Dovgalyuk/MRRSoundDecoder/esp32/components/sd/sd.c

/* SD card and FAT filesystem example.
   This example uses SPI peripheral to communicate with SD card.

   This example code is in the Public Domain (or CC0 licensed, at your option.)

   Unless required by applicable law or agreed to in writing, this
   software is distributed on an "AS IS" BASIS, WITHOUT WARRANTIES OR
   CONDITIONS OF ANY KIND, either express or implied.
*/

#include <string.h>
#include <sys/unistd.h>
#include <sys/stat.h>
#include "esp_vfs_fat.h"
#include "sdmmc_cmd.h"
//#include "sd_test_io.h"
#if SOC_SDMMC_IO_POWER_EXTERNAL
#include "sd_pwr_ctrl_by_on_chip_ldo.h"
#endif

static const char *TAG = "sd";

// Pin assignments can be set in menuconfig, see "SD SPI Example Configuration" menu.
// You can also change the pin assignments here by changing the following 4 lines.
#define PIN_NUM_MISO  CONFIG_SD_PIN_MISO
#define PIN_NUM_MOSI  CONFIG_SD_PIN_MOSI
#define PIN_NUM_CLK   CONFIG_SD_PIN_CLK
#define PIN_NUM_CS    CONFIG_SD_PIN_CS

void sd_init(const char *mount_point)
{
    esp_err_t ret;

    // Options for mounting the filesystem.
    esp_vfs_fat_sdmmc_mount_config_t mount_config = {
        .format_if_mount_failed = false,
        .max_files = 3,
        .allocation_unit_size = 8 * 1024
    };
    sdmmc_card_t *card;
    ESP_LOGI(TAG, "Initializing SD card");

    // Use settings defined above to initialize SD card and mount FAT filesystem.
    // Note: esp_vfs_fat_sdmmc/sdspi_mount is all-in-one convenience functions.
    // Please check its source code and implement error recovery when developing
    // production applications.
    ESP_LOGI(TAG, "Using SPI peripheral");

    // By default, SD card frequency is initialized to SDMMC_FREQ_DEFAULT (20MHz)
    // For setting a specific frequency, use host.max_freq_khz (range 400kHz - 20MHz for SDSPI)
    // Example: for fixed frequency of 10MHz, use host.max_freq_khz = 10000;
    sdmmc_host_t host = SDSPI_HOST_DEFAULT();

    // For SoCs where the SD power can be supplied both via an internal or external (e.g. on-board LDO) power supply.
    // When using specific IO pins (which can be used for ultra high-speed SDMMC) to connect to the SD card
    // and the internal LDO power supply, we need to initialize the power supply first.
#if CONFIG_EXAMPLE_SD_PWR_CTRL_LDO_INTERNAL_IO
    sd_pwr_ctrl_ldo_config_t ldo_config = {
        .ldo_chan_id = CONFIG_EXAMPLE_SD_PWR_CTRL_LDO_IO_ID,
    };
    sd_pwr_ctrl_handle_t pwr_ctrl_handle = NULL;

    ret = sd_pwr_ctrl_new_on_chip_ldo(&ldo_config, &pwr_ctrl_handle);
    if (ret != ESP_OK) {
        ESP_LOGE(TAG, "Failed to create a new on-chip LDO power control driver");
        return;
    }
    host.pwr_ctrl_handle = pwr_ctrl_handle;
#endif

    spi_bus_config_t bus_cfg = {
        .mosi_io_num = PIN_NUM_MOSI,
        .miso_io_num = PIN_NUM_MISO,
        .sclk_io_num = PIN_NUM_CLK,
        .quadwp_io_num = -1,
        .quadhd_io_num = -1,
        .max_transfer_sz = 4000,
    };

    /* Enable pullup for faster operation */
    gpio_set_direction(PIN_NUM_CLK, GPIO_MODE_INPUT_OUTPUT_OD);
    gpio_set_direction(PIN_NUM_CS, GPIO_MODE_INPUT_OUTPUT_OD);
    gpio_set_direction(PIN_NUM_MOSI, GPIO_MODE_INPUT_OUTPUT_OD);
    gpio_set_direction(PIN_NUM_MISO, GPIO_MODE_INPUT_OUTPUT_OD);
    gpio_pullup_en(PIN_NUM_CLK);
    gpio_pullup_en(PIN_NUM_CS);
    gpio_pullup_en(PIN_NUM_MOSI);
    gpio_pullup_en(PIN_NUM_MISO);

    ret = spi_bus_initialize(host.slot, &bus_cfg, SDSPI_DEFAULT_DMA);
    if (ret != ESP_OK) {
        ESP_LOGE(TAG, "Failed to initialize bus.");
        return;
    }

    // This initializes the slot without card detect (CD) and write protect (WP) signals.
    // Modify slot_config.gpio_cd and slot_config.gpio_wp if your board has these signals.
    sdspi_device_config_t slot_config = SDSPI_DEVICE_CONFIG_DEFAULT();
    slot_config.gpio_cs = PIN_NUM_CS;
    slot_config.host_id = host.slot;

    ESP_LOGI(TAG, "Mounting filesystem");
    ret = esp_vfs_fat_sdspi_mount(mount_point, &host, &slot_config, &mount_config, &card);

    if (ret != ESP_OK) {
        if (ret == ESP_FAIL) {
            ESP_LOGE(TAG, "Failed to mount filesystem. ");
        } else {
            ESP_LOGE(TAG, "Failed to initialize the card (%s). "
                     "Make sure SD card lines have pull-up resistors in place.", esp_err_to_name(ret));
        }
        return;
    }
    ESP_LOGI(TAG, "Filesystem mounted");

    // Card has been initialized, print its properties
    sdmmc_card_print_info(stdout, card);
#if 0
    // All done, unmount partition and disable SPI peripheral
    esp_vfs_fat_sdcard_unmount(mount_point, card);
    ESP_LOGI(TAG, "Card unmounted");

    //deinitialize the bus after all devices are removed
    spi_bus_free(host.slot);

    // Deinitialize the power control driver if it was used
#if CONFIG_EXAMPLE_SD_PWR_CTRL_LDO_INTERNAL_IO
    ret = sd_pwr_ctrl_del_on_chip_ldo(pwr_ctrl_handle);
    if (ret != ESP_OK) {
        ESP_LOGE(TAG, "Failed to delete the on-chip LDO power control driver");
        return;
    }
#endif
#endif
}
