Dovgalyuk/MRRSoundDecoder/include/engine.h

#ifndef ENGINE_H
#define ENGINE_H

#include <stdint.h>
#include "vm.h"

#define ENGINE_THROTTLE_STEPS 28

void engine_init(void);
void engine_tick(uint32_t t);

void engine_set_throttle(uint8_t v);
uint8_t engine_get_speed(void);
uint8_t engine_get_speed_step(void);
/* Returns true for forward */
bool engine_get_direction(void);
void engine_set_direction(bool d);
void engine_stop(void);
void engine_hw_stop(void);
void engine_brake(void);
bool engine_can_accelerate(void);

char *engine_get_status(void);

#endif
