Dovgalyuk/MRRSoundDecoder/include/vm.h

#ifndef VM_H
#define VM_H

#include <stdint.h>
#include <stdbool.h>
#include <stdio.h>

#define VM_SLOTS         128
#define VM_FUNCTION_KEYS 32

typedef struct Slot Slot;
typedef struct Schedule Schedule;

typedef enum VMCommand {
    VM_CMD_NONE = 0,
    VM_CMD_STOP,
    VM_CMD_BRAKE,
    VM_CMD_SET_THROTTLE,
    VM_CMD_SET_DIRECTION,
    VM_CMD_SET_FUNCTION_STATE,
} VMCommand;

void vm_init(void);
void vm_clear(void);
void vm_reset(void);
bool vm_load_slot(FILE *f);

uint8_t vm_get_var(uint16_t addr);
void vm_set_var(uint16_t addr, uint8_t val);

void vm_set_slot_var(uint8_t id, uint16_t addr, uint8_t val);
uint8_t vm_get_slot_var(uint8_t id, uint16_t addr);

void vm_tick(uint32_t t);
void vm_reset_trigger(void);

void vm_set_function_key(uint8_t f, bool v);
bool vm_get_function_key(uint8_t f);

void vm_queue_command(VMCommand cmd, uint16_t param1, uint16_t param2);

#endif
